akkoyun/B202AA-PCIe/Design Files/Output/Below Image/B202AA-PCIe.jpg

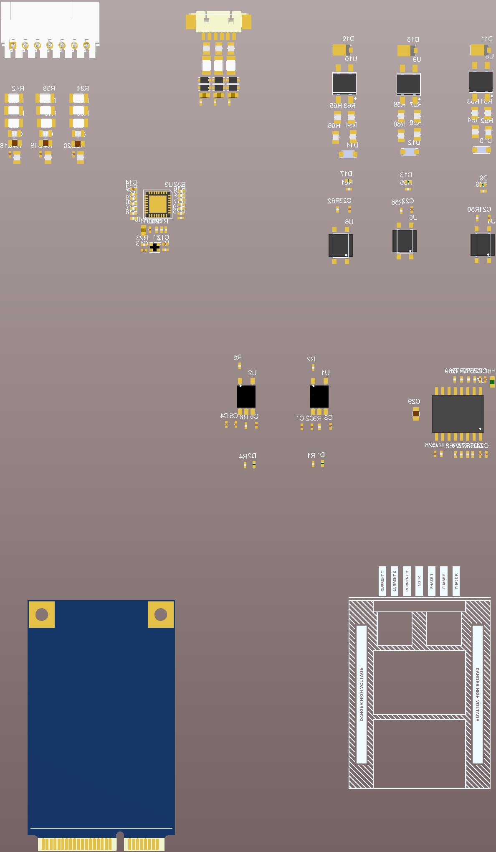
Design Files/Output/Below Image/B202AA-PCIe.jpg
