akkoyun/B202AA-PCIe/Design Files/Output/Above Image/B202AA-PCIe.jpg

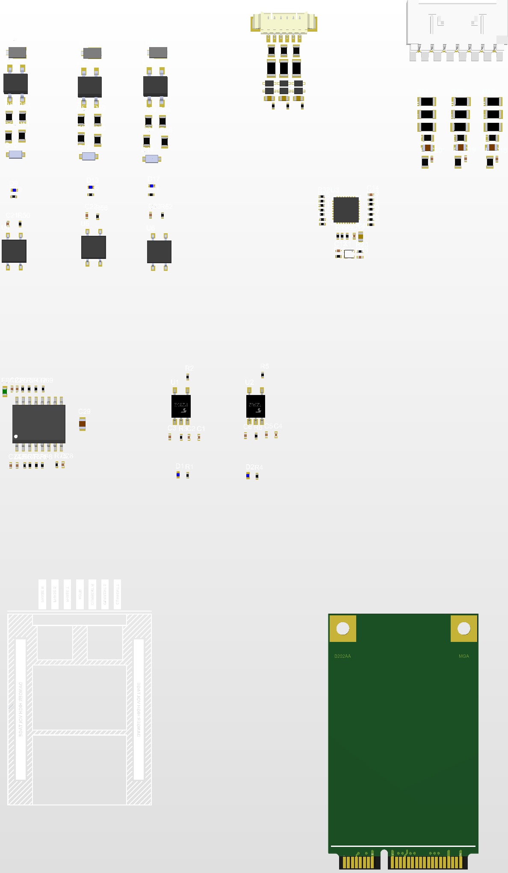
Design Files/Output/Above Image/B202AA-PCIe.jpg
